88markus88/ESP32_ePaper_Barograph/src/ePaperBLE.h

#ifndef _ePaperBLE_H
#define _ePaperBLE_H

//************** module defines *************************/

//************** module global variables *************************/

//************** function prototypes *************************/

#endif // _ePaperBLE_H
